valerionew/53xLIDAR/firmware/Core/VL53L1X_API/platform/vl53l1_platform.c

/* 
* This file is part of VL53L1 Platform 
* 
* Copyright (c) 2016, STMicroelectronics - All Rights Reserved 
* 
* License terms: BSD 3-clause "New" or "Revised" License. 
* 
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
* 3. Neither the name of the copyright holder nor the names of its contributors 
* may be used to endorse or promote products derived from this software 
* without specific prior written permission. 
* 
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
*/

#include "vl53l1_platform.h"
#include <string.h>
#include <time.h>
#include <math.h>

#include "stm32f4xx_hal.h"

#ifndef HAL_I2C_MODULE_ENABLED
#warning "HAL I2C module must be enable "
#endif

#define I2C_TIME_OUT_BASE   10
#define I2C_TIME_OUT_BYTE   1

uint8_t _I2CBuffer[256];

//horrible hack because those libs have become worse than before and i need to squize all info (i2c bus and address) in an uint16
extern I2C_HandleTypeDef hi2c1;
extern I2C_HandleTypeDef hi2c2;
I2C_HandleTypeDef *hw[2] = {&hi2c1, &hi2c2};

int _I2CWrite(uint16_t dev, uint8_t *pdata, uint32_t count) {
    int status;
    int i2c_time_out = I2C_TIME_OUT_BASE+ count* I2C_TIME_OUT_BYTE;

    status = HAL_I2C_Master_Transmit(hw[dev >> 8], dev & 0xFF, pdata, count, i2c_time_out);
    if (status) {
        //VL6180x_ErrLog("I2C error 0x%x %d len", dev, count);
    }
    return status;
}

int _I2CRead(uint16_t dev, uint8_t *pdata, uint32_t count) {
    int status;
    int i2c_time_out = I2C_TIME_OUT_BASE+ count* I2C_TIME_OUT_BYTE;

    status = HAL_I2C_Master_Receive(hw[dev >> 8], (dev & 0xFF)|1, pdata, count, i2c_time_out);
    if (status) {
        //VL6180x_ErrLog("I2C error 0x%x %d len", dev, count);
    }
    return status;
}

int8_t VL53L1_WriteMulti( uint16_t dev, uint16_t index, uint8_t *pdata, uint32_t count) {
    int status_int;
    VL53L1X_Error err = VL53L1_ERROR_NONE;
    if (count > sizeof(_I2CBuffer) - 1) {
        return VL53L1_ERROR_INVALID_PARAMS;
    }
    _I2CBuffer[0] = index>>8;
    _I2CBuffer[1] = index&0xFF;
    memcpy(&_I2CBuffer[2], pdata, count);
    status_int = _I2CWrite(dev, _I2CBuffer, count + 2);
    if (status_int != 0) {
        err = VL53L1_ERROR_CONTROL_INTERFACE;
    }
    return err;
}

int8_t VL53L1_ReadMulti(uint16_t dev, uint16_t index, uint8_t *pdata, uint32_t count){
    VL53L1X_Error err = VL53L1_ERROR_NONE;
    int32_t status_int;

    _I2CBuffer[0] = index>>8;
    _I2CBuffer[1] = index&0xFF;
    status_int = _I2CWrite(dev, _I2CBuffer, 2);
    if (status_int != 0) {
        err = VL53L1_ERROR_CONTROL_INTERFACE;
        goto done;
    }
    status_int = _I2CRead(dev, pdata, count);
    if (status_int != 0) {
        err = VL53L1_ERROR_CONTROL_INTERFACE;
    }
done:
    return err;
}

int8_t VL53L1_WrByte(uint16_t dev, uint16_t index, uint8_t data) {
    VL53L1X_Error err = VL53L1_ERROR_NONE;
    int32_t status_int;

    _I2CBuffer[0] = index>>8;
    _I2CBuffer[1] = index&0xFF;
    _I2CBuffer[2] = data;

    status_int = _I2CWrite(dev, _I2CBuffer, 3);
    if (status_int != 0) {
        err = VL53L1_ERROR_CONTROL_INTERFACE;
    }
    return err;
}

int8_t VL53L1_WrWord(uint16_t dev, uint16_t index, uint16_t data) {
    VL53L1X_Error err = VL53L1_ERROR_NONE;
    int32_t status_int;

    _I2CBuffer[0] = index>>8;
    _I2CBuffer[1] = index&0xFF;
    _I2CBuffer[2] = data >> 8;
    _I2CBuffer[3] = data & 0x00FF;

    status_int = _I2CWrite(dev, _I2CBuffer, 4);
    if (status_int != 0) {
        err = VL53L1_ERROR_CONTROL_INTERFACE;
    }
    return err;
}

int8_t VL53L1_WrDWord(uint16_t dev, uint16_t index, uint32_t data) {
    VL53L1X_Error err = VL53L1_ERROR_NONE;
    int32_t status_int;
    _I2CBuffer[0] = index>>8;
    _I2CBuffer[1] = index&0xFF;
    _I2CBuffer[2] = (data >> 24) & 0xFF;
    _I2CBuffer[3] = (data >> 16) & 0xFF;
    _I2CBuffer[4] = (data >> 8)  & 0xFF;
    _I2CBuffer[5] = (data >> 0 ) & 0xFF;

    status_int = _I2CWrite(dev, _I2CBuffer, 6);
    if (status_int != 0) {
        err = VL53L1_ERROR_CONTROL_INTERFACE;
    }
    return err;
}

int8_t VL53L1_RdByte(uint16_t dev, uint16_t index, uint8_t *data) {
    VL53L1X_Error err = VL53L1_ERROR_NONE;
    int32_t status_int;

    _I2CBuffer[0] = index>>8;
    _I2CBuffer[1] = index&0xFF;

    status_int = _I2CWrite(dev, _I2CBuffer, 2);
    if( status_int ){
        err = VL53L1_ERROR_CONTROL_INTERFACE;
        goto done;
    }
    status_int = _I2CRead(dev, data, 1);
    if (status_int != 0) {
        err = VL53L1_ERROR_CONTROL_INTERFACE;
    }
done:
    return err;
}

int8_t VL53L1_RdWord(uint16_t dev, uint16_t index, uint16_t *data) {
    VL53L1X_Error err = VL53L1_ERROR_NONE;
    int32_t status_int;

    _I2CBuffer[0] = index>>8;
    _I2CBuffer[1] = index&0xFF;

    status_int = _I2CWrite(dev, _I2CBuffer, 2);

    if( status_int ){
        err = VL53L1_ERROR_CONTROL_INTERFACE;
        goto done;
    }
    status_int = _I2CRead(dev, _I2CBuffer, 2);
    if (status_int != 0) {
        err = VL53L1_ERROR_CONTROL_INTERFACE;
        goto done;
    }

    *data = ((uint16_t)_I2CBuffer[0]<<8) + (uint16_t)_I2CBuffer[1];
done:
    return err;
}

int8_t VL53L1_RdDWord(uint16_t dev, uint16_t index, uint32_t *data) {
    VL53L1X_Error err = VL53L1_ERROR_NONE;
    int32_t status_int;

    _I2CBuffer[0] = index>>8;
    _I2CBuffer[1] = index&0xFF;

    status_int = _I2CWrite(dev, _I2CBuffer, 2);
    if (status_int != 0) {
        err = VL53L1_ERROR_CONTROL_INTERFACE;
        goto done;
    }
    status_int = _I2CRead(dev, _I2CBuffer, 4);
    if (status_int != 0) {
        err = VL53L1_ERROR_CONTROL_INTERFACE;
        goto done;
    }

    *data = ((uint32_t)_I2CBuffer[0]<<24) + ((uint32_t)_I2CBuffer[1]<<16) + ((uint32_t)_I2CBuffer[2]<<8) + (uint32_t)_I2CBuffer[3];

done:
    return err;
}

int8_t VL53L1_WaitMs(uint16_t dev, int32_t wait_ms){
    (void)dev;
    HAL_Delay(wait_ms);
    return VL53L1_ERROR_NONE;
}
